jollie-fin/paillaas/board/prototype/motherboard_mini-itx_before_adding_io/motherboard_mini-itx.ods

Sheet: motherboard_mini-itx
Source: |  | /home/phi/dev/paillaaS/board/prototype/motherboard_mini-itx/motherboard_mini-itx.sch
Date: |  | mar. 13 avril 2021 10:53:32
Tool: |  | Eeschema 5.1.9-73d0e3b20d~88~ubuntu20.04.1
Generator: |  | /usr/share/kicad/plugins/bom_csv_grouped_by_value.py
Component Count: |  | 181
Individual Components:
Item |  | Qty |  |  |  |  | Reference(s) | Value | LibPart | Footprint | Datasheet
 |  |  |  |  |  |  | C1 | 100n | Device:C | Capacitor_SMD:C_0402_1005Metric | ~
 |  |  |  |  |  |  | C2 | 100n | Device:C | Capacitor_SMD:C_0402_1005Metric | ~
 |  |  |  |  |  |  | C3 | 100n | Device:C | Capacitor_SMD:C_0402_1005Metric | ~
 |  |  |  |  |  |  | C4 | 10u | Device:C | Capacitor_SMD:C_0402_1005Metric | ~
 |  |  |  |  |  |  | C5 | 100n | Device:C | Capacitor_SMD:C_0402_1005Metric | ~
 |  |  |  |  |  |  | C6 | 100n | Device:C | Capacitor_SMD:C_0402_1005Metric | ~
 |  |  |  |  |  |  | C7 | 100n | Device:C | Capacitor_SMD:C_0402_1005Metric | ~
 |  |  |  |  |  |  | C8 | 100n | Device:C | Capacitor_SMD:C_0402_1005Metric | ~
 |  |  |  |  |  |  | C9 | 10u | Device:C | Capacitor_SMD:C_0805_2012Metric | ~
 |  |  |  |  |  |  | C10 | 22n | Device:C | Capacitor_SMD:C_0402_1005Metric | ~
 |  |  |  |  |  |  | C11 | 100n | Device:C | Capacitor_SMD:C_0402_1005Metric | ~
 |  |  |  |  |  |  | C12 | 10u | Device:C | Capacitor_SMD:C_0805_2012Metric | ~
 |  |  |  |  |  |  | C13 | 100n | Device:C | Capacitor_SMD:C_0402_1005Metric | ~
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
 |  |  |  |  |  |  | D1 | RED | Device:LED | LED_SMD:LED_0603_1608Metric | ~
 |  |  |  |  |  |  | D2 | RED | Device:LED | LED_SMD:LED_0603_1608Metric | ~
 |  |  |  |  |  |  | D4 | RED | Device:LED | LED_SMD:LED_0603_1608Metric | ~
 |  |  |  |  |  |  | H1 | MountingHole_Pad | Mechanical:MountingHole_Pad | MountingHole:MountingHole_3.2mm_M3_Pad_Via | ~
 |  |  |  |  |  |  | H2 | MountingHole_Pad | Mechanical:MountingHole_Pad | MountingHole:MountingHole_3.2mm_M3_Pad_Via | ~
 |  |  |  |  |  |  | H3 | MountingHole_Pad | Mechanical:MountingHole_Pad | MountingHole:MountingHole_3.2mm_M3_Pad_Via | ~
 |  |  |  |  |  |  | H4 | MountingHole_Pad | Mechanical:MountingHole_Pad | MountingHole:MountingHole_3.2mm_M3_Pad_Via | ~
 |  |  |  |  |  |  | J1 | RJMG2310228A0ER | library:RJMG2310228A0ER | library:RJMG2310228A0ER | https://cdn.amphenol-icc.com/media/wysiwyg/files/documentation/datasheet/inputoutput/io_rjmag_stacked.pdf
 |  |  |  |  |  |  | J2 | Conn_01x22_MountingPin | Connector_Generic_MountingPin:Conn_01x22_MountingPin | Connector_FFC-FPC:TE_2-1734839-2_1x22-1MP_P0.5mm_Horizontal | ~
 |  |  |  |  |  |  | J3 | Conn_01x22_MountingPin | Connector_Generic_MountingPin:Conn_01x22_MountingPin | Connector_FFC-FPC:TE_2-1734839-2_1x22-1MP_P0.5mm_Horizontal | ~
 |  |  |  |  |  |  | J4 | Conn_02x20_Odd_Even | Connector_Generic:Conn_02x20_Odd_Even | Connector_IDC:IDC-Header_2x20_P2.54mm_Vertical | ~
 |  |  |  |  |  |  | J5 | Conn_02x08_Odd_Even | Connector_Generic:Conn_02x08_Odd_Even | Connector_PinHeader_2.54mm:PinHeader_2x08_P2.54mm_Vertical | ~
 |  |  |  |  |  |  | J6 | Conn_02x12_Top_Bottom | Connector_Generic:Conn_02x12_Top_Bottom | Connector_Molex:Molex_Mini-Fit_Jr_5566-24A_2x12_P4.20mm_Vertical | ~
 |  |  |  |  |  |  | J7 | Conn_02x04_Top_Bottom | Connector_Generic:Conn_02x04_Top_Bottom | Connector_Molex:Molex_Mini-Fit_Jr_5566-08A_2x04_P4.20mm_Vertical | ~
 |  |  |  |  |  |  | J8 | Conn_02x20_Odd_Even | Connector_Generic:Conn_02x20_Odd_Even | Connector_IDC:IDC-Header_2x20_P2.54mm_Vertical | ~
 |  |  |  |  |  |  | J9 | Conn_02x20_Odd_Even | Connector_Generic:Conn_02x20_Odd_Even | Connector_IDC:IDC-Header_2x20_P2.54mm_Vertical | ~
 |  |  |  |  |  |  | J10 | Conn_02x07_Odd_Even | Connector_Generic:Conn_02x07_Odd_Even | Connector_PinHeader_2.54mm:PinHeader_2x07_P2.54mm_Vertical | ~
 |  |  |  |  |  |  | J11 | Conn_01x22_MountingPin | Connector_Generic_MountingPin:Conn_01x22_MountingPin | Connector_FFC-FPC:TE_2-1734839-2_1x22-1MP_P0.5mm_Horizontal | ~
 |  |  |  |  |  |  | J12 | HDMI_A | Connector:HDMI_A | library:HDMI_RAHHD19TR | https://en.wikipedia.org/wiki/HDMI
 |  |  |  |  |  |  | J13 | USB_B_Micro | Connector:USB_B_Micro | Connector_USB:USB_Micro-B_Amphenol_10103594-0001LF_Horizontal | ~
 |  |  |  |  |  |  | R1 | 1k8 | Device:R | Resistor_SMD:R_0402_1005Metric | ~
 |  |  |  |  |  |  | R2 | 1k8 | Device:R | Resistor_SMD:R_0402_1005Metric | ~
 |  |  |  |  |  |  | R3 | 1k8 | Device:R | Resistor_SMD:R_0402_1005Metric | ~
 |  |  |  |  |  |  | R4 | 30 | Device:R | Resistor_SMD:R_0402_1005Metric | ~
 |  |  |  |  |  |  | R5 | 30 | Device:R | Resistor_SMD:R_0402_1005Metric | ~
 |  |  |  |  |  |  | R6 | 150 | Device:R | Resistor_SMD:R_0402_1005Metric | ~
 |  |  |  |  |  |  | R7 | 150 | Device:R | Resistor_SMD:R_0402_1005Metric | ~
 |  |  |  |  |  |  | R8 | 150 | Device:R | Resistor_SMD:R_0402_1005Metric | ~
 |  |  |  |  |  |  | R9 | 150 | Device:R | Resistor_SMD:R_0402_1005Metric | ~
 |  |  |  |  |  |  | R10 | 150 | Device:R | Resistor_SMD:R_0402_1005Metric | ~
 |  |  |  |  |  |  | R11 | 150 | Device:R | Resistor_SMD:R_0402_1005Metric | ~
 |  |  |  |  |  |  | R12 | 150 | Device:R | Resistor_SMD:R_0402_1005Metric | ~
 |  |  |  |  |  |  | R13 | 150 | Device:R | Resistor_SMD:R_0402_1005Metric | ~
 |  |  |  |  |  |  | R14 | 1K8 | Device:R | Resistor_SMD:R_0402_1005Metric | ~
 |  |  |  |  |  |  | R15 | 1K8 | Device:R | Resistor_SMD:R_0402_1005Metric | ~
 |  |  |  |  |  |  | R16 | 1k8 | Device:R | Resistor_SMD:R_0402_1005Metric | ~
 |  |  |  |  |  |  | R17 | 1K8 | Device:R | Resistor_SMD:R_0402_1005Metric | ~
 |  |  |  |  |  |  | R18 | 150 | Device:R | Resistor_SMD:R_0402_1005Metric | ~
 |  |  |  |  |  |  | R19 | 150 | Device:R | Resistor_SMD:R_0402_1005Metric | ~
 |  |  |  |  |  |  | R20 | 150 | Device:R | Resistor_SMD:R_0402_1005Metric | ~
 |  |  |  |  |  |  | R21 | 150 | Device:R | Resistor_SMD:R_0402_1005Metric | ~
 |  |  |  |  |  |  | R22 | 150 | Device:R | Resistor_SMD:R_0402_1005Metric | ~
 |  |  |  |  |  |  | R23 | 150 | Device:R | Resistor_SMD:R_0402_1005Metric | ~
 |  |  |  |  |  |  | R24 | 150 | Device:R | Resistor_SMD:R_0402_1005Metric | ~
 |  |  |  |  |  |  | R25 | 150 | Device:R | Resistor_SMD:R_0402_1005Metric | ~
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
 |  |  |  |  |  |  | R79 | 1k8 | Device:R | Resistor_SMD:R_0402_1005Metric | ~
 |  |  |  |  |  |  | R80 | 1k8 | Device:R | Resistor_SMD:R_0402_1005Metric | ~
 |  |  |  |  |  |  | R81 | 1k8 | Device:R | Resistor_SMD:R_0402_1005Metric | ~
 |  |  |  |  |  |  | R82 | 0.21 | Device:R | Resistor_SMD:R_1206_3216Metric | ~
 |  |  |  |  |  |  | SW1 | FSUSB30MUX | library:FSUSB30MUX | Package_SO:MSOP-10_3x3mm_P0.5mm | https://www.onsemi.com/pdf/datasheet/fsusb30-d.pdf
 |  |  |  |  |  |  | U1 | Compute_Module_4_Functional | Raspberry_Pi_Compute_Module_4:Compute_Module_4_Functional | RPi_Compute_Module_4:Raspberry-Pi-4-Compute-Module
 |  |  |  |  |  |  | U2 | 74LVC125 | 74xx:74LVC125 | Package_SO:TSSOP-14_4.4x5mm_P0.65mm | http://www.ti.com/lit/gpn/sn74LVC125
 |  |  |  |  |  |  | U3 | MCP3008 | Analog_ADC:MCP3008 | Package_SO:SOIC-16_3.9x9.9mm_P1.27mm | http://ww1.microchip.com/downloads/en/DeviceDoc/21295d.pdf
 |  |  |  |  |  |  | U4 | 74HCT244 | 74xx:74HC244 | Package_SO:TSSOP-20_4.4x6.5mm_P0.65mm | http://www.ti.com/lit/gpn/sn74LVC125
 |  |  |  |  |  |  | U5 | 74HCT244 | 74xx:74HC244 | Package_SO:TSSOP-20_4.4x6.5mm_P0.65mm | http://www.ti.com/lit/gpn/sn74LVC125
 |  |  |  |  |  |  | U6 | 74HC595 | 74xx:74HC595 | Package_SO:SSOP-16_5.3x6.2mm_P0.65mm | http://www.ti.com/lit/ds/symlink/sn74hc595.pdf
 |  |  |  |  |  |  | U7 | TBD62783A | Transistor_Array:TBD62783A | Package_SO:SSOP-18_4.4x6.5mm_P0.65mm | http://toshiba.semicon-storage.com/info/docget.jsp?did=30523&prodName=TBD62783APG
 |  |  |  |  |  |  | U8 | TMC5130A-TA | TMC5130:TMC5130A-TA | Package_QFP:TQFP-48-1EP_7x7mm_P0.5mm_EP5x5mm_ThermalVias
 |  |  |  |  |  |  | U9 | TMC5130A-TA | TMC5130:TMC5130A-TA | Package_QFP:TQFP-48-1EP_7x7mm_P0.5mm_EP5x5mm_ThermalVias
 |  |  |  |  |  |  | U10 | TMC5130A-TA | TMC5130:TMC5130A-TA | Package_QFP:TQFP-48-1EP_7x7mm_P0.5mm_EP5x5mm_ThermalVias
 |  |  |  |  |  |  | U11 | TMC5130A-TA | TMC5130:TMC5130A-TA | Package_QFP:TQFP-48-1EP_7x7mm_P0.5mm_EP5x5mm_ThermalVias
 |  |  |  |  |  |  | U12 | TMC5130A-TA | TMC5130:TMC5130A-TA | Package_QFP:TQFP-48-1EP_7x7mm_P0.5mm_EP5x5mm_ThermalVias
 |  |  |  |  |  |  | U13 | AP22804AW5 | Power_Management:AP22804AW5 | Package_TO_SOT_SMD:SOT-23-5 | https://www.diodes.com/assets/Datasheets/AP22804_14.pdf
Collated Components:
Item | Ppu | Qty |  | Subtotal | Accumul | Mouser | Reference(s) | Value | LibPart | Footprint | Datasheet
1 | 0.013 € | 26 | 26 | 0.34 € | 0.34 € | 581-0402YD104MAT2A | C1, C2, C3, C5, C6, C7, C8, C11, C13, C14, C17, C20, C22, C23, C26, C29, C31, C32, C35, C38, C40, C41, C44, C47, C49, C50 | 100n | Device:C | Capacitor_SMD:C_0402_1005Metric | ~
3 | 0.025 € | 28 | 28 | 0.70 € | 1.04 € | 963-EMK105BJ105KVHF | C4, C9, C12, C15, C16, C18, C21, C24, C25, C27, C30, C33, C34, C36, C39, C42, C43, C45, C48, C51, C52, C53, C54, C55, C56, C62, C63, C64 | 10u | Device:C | Capacitor_SMD:C_0805_2012Metric | ~
4 | 0.030 € | 6 | 6 | 0.18 € | 1.22 € | 80-C0603C223K5R | C10, C19, C28, C37, C46, C61 | 22n | Device:C | Capacitor_SMD:C_0402_1005Metric | ~
5 | 0.119 € | 5 | 5 | 0.60 € | 1.81 € | 140-REA101M1HBK0811P | C57, C58, C59, C60, C65 | 100u | Device:CP | Capacitor_THT:CP_Radial_D8.0mm_P3.50mm | ~
6 | 0.117 € | 3 | 3 | 0.35 € | 2.16 € | 710-150060GS75000 | D1, D2, D4 | RED | Device:LED | LED_SMD:LED_0603_1608Metric | ~
7 |  | 4 | 0 | 0.00 € | 2.16 € |  | H1, H2, H3, H4 | MountingHole_Pad | Mechanical:MountingHole_Pad | MountingHole:MountingHole_3.2mm_M3_Pad_Via | ~
8 | 3.450 € | 1 | 1 | 3.45 € | 5.61 € | 571-6116151-1 | J1 | RJMG2310228A0ER | library:RJMG2310228A0ER | library:RJMG2310228A0ER | https://cdn.amphenol-icc.com/media/wysiwyg/files/documentation/datasheet/inputoutput/io_rjmag_stacked.pdf
9 | 0.504 € | 3 | 3 | 1.51 € | 7.13 € | 538-501951-2230 | J2, J3, J11 | Conn_01x22_MountingPin | Connector_Generic_MountingPin:Conn_01x22_MountingPin | Connector_FFC-FPC:TE_2-1734839-2_1x22-1MP_P0.5mm_Horizontal | ~
10 | 0.932 € | 3 | 3 | 2.80 € | 9.92 € | 517-30340-6002 | J4, J8, J9 | Conn_02x20_Odd_Even | Connector_Generic:Conn_02x20_Odd_Even | Connector_IDC:IDC-Header_2x20_P2.54mm_Vertical | ~
11 |  | 1 | 0 | 0.00 € | 9.92 € |  | J5 | Conn_02x08_Odd_Even | Connector_Generic:Conn_02x08_Odd_Even | Connector_PinHeader_2.54mm:PinHeader_2x08_P2.54mm_Vertical | ~
12 | 0.966 € | 1 | 1 | 0.97 € | 10.89 € | 571-215860394 | J6 | Conn_02x12_Top_Bottom | Connector_Generic:Conn_02x12_Top_Bottom | Connector_Molex:Molex_Mini-Fit_Jr_5566-24A_2x12_P4.20mm_Vertical | ~
13 | 0.512 € | 1 | 1 | 0.51 € | 11.40 € | 571-15860398 | J7 | Conn_02x04_Top_Bottom | Connector_Generic:Conn_02x04_Top_Bottom | Connector_Molex:Molex_Mini-Fit_Jr_5566-08A_2x04_P4.20mm_Vertical | ~
14 |  | 1 | 0 | 0.00 € | 11.40 € |  | J10 | Conn_02x07_Odd_Even | Connector_Generic:Conn_02x07_Odd_Even | Connector_PinHeader_2.54mm:PinHeader_2x07_P2.54mm_Vertical | ~
15 | 0.529 € | 1 | 1 | 0.53 € | 11.93 € | 502-RAHHD19TR | J12 | HDMI_A | Connector:HDMI_A | library:HDMI_RAHHD19TR | https://en.wikipedia.org/wiki/HDMI
16 | 0.019 € | 1 | 1 | 0.02 € | 11.95 € |  | J13 | USB_B_Micro | Connector:USB_B_Micro | Connector_USB:USB_Micro-B_Amphenol_10103594-0001LF_Horizontal | ~
17 | 0.009 € | 32 | 32 | 0.29 € | 12.24 € |  | R1, R2, R3, R16, R38, R39, R41, R45, R46, R47, R48, R49, R53, R54, R55, R56, R57, R61, R62, R63, R64, R65, R69, R70, R71, R72, R73, R77, R78, R79, R80, R81 | 1k8 | Device:R | Resistor_SMD:R_0402_1005Metric | ~
18 | 0.019 € | 7 | 7 | 0.13 € | 12.37 € |  | R4, R5, R26, R27, R28, R29, R42 | 30 | Device:R | Resistor_SMD:R_0402_1005Metric | ~
19 | 0.009 € | 24 | 24 | 0.22 € | 12.59 € |  | R6, R7, R8, R9, R10, R11, R12, R13, R18, R19, R20, R21, R22, R23, R24, R25, R30, R31, R32, R33, R34, R35, R36, R37 | 150 | Device:R | Resistor_SMD:R_0402_1005Metric | ~
20 | 0.019 € | 4 | 4 | 0.08 € | 12.66 € |  | R14, R15, R17, R40 | 1K8 | Device:R | Resistor_SMD:R_0402_1005Metric | ~
21 | 0.019 € | 5 | 5 | 0.10 € | 12.76 € |  | R43, R51, R59, R67, R75 | 10 | Device:R | Resistor_SMD:R_0402_1005Metric | ~
22 | 0.058 € | 10 | 10 | 0.58 € | 13.34 € | 588-KDV12DR220ET | R44, R50, R52, R58, R60, R66, R68, R74, R76, R82 | 0.22 | Device:R | Resistor_SMD:R_1206_3216Metric | ~
23 | 0.445 € | 1 | 1 | 0.45 € | 13.78 € | 512-FSUSB30MUX | SW1 | FSUSB30MUX | library:FSUSB30MUX | Package_SO:MSOP-10_3x3mm_P0.5mm | https://www.onsemi.com/pdf/datasheet/fsusb30-d.pdf
24 | 1.820 € | 2 | 2 | 3.64 € | 17.42 € | 798-DF40HC30100DS451 | U1 | Compute_Module_4_Functional | Raspberry_Pi_Compute_Module_4:Compute_Module_4_Functional | RPi_Compute_Module_4:Raspberry-Pi-4-Compute-Module
25 | 1.950 € | 1 | 1 | 1.95 € | 19.37 € |  | U2 | 74LVC125 | 74xx:74LVC125 | Package_SO:TSSOP-14_4.4x5mm_P0.65mm | http://www.ti.com/lit/gpn/sn74LVC125
26 | 0.296 € | 1 | 1 | 0.30 € | 19.67 € |  | U3 | MCP3008 | Analog_ADC:MCP3008 | Package_SO:SOIC-16_3.9x9.9mm_P1.27mm | http://ww1.microchip.com/downloads/en/DeviceDoc/21295d.pdf
27 | 0.480 € | 2 | 2 | 0.96 € | 20.63 € |  | U4, U5 | 74HCT244 | 74xx:74HC244 | Package_SO:TSSOP-20_4.4x6.5mm_P0.65mm | http://www.ti.com/lit/gpn/sn74LVC125
28 | 0.500 € | 1 | 1 | 0.50 € | 21.13 € |  | U6 | 74HC595 | 74xx:74HC595 | Package_SO:SSOP-16_5.3x6.2mm_P0.65mm | http://www.ti.com/lit/ds/symlink/sn74hc595.pdf
29 | 1.400 € | 1 | 1 | 1.40 € | 22.53 € |  | U7 | TBD62783A | Transistor_Array:TBD62783A | Package_SO:SSOP-18_4.4x6.5mm_P0.65mm | http://toshiba.semicon-storage.com/info/docget.jsp?did=30523&prodName=TBD62783APG
30 | 4.270 € | 5 | 5 | 21.35 € | 43.88 € |  | U8, U9, U10, U11, U12 | TMC5130A-TA | TMC5130:TMC5130A-TA | Package_QFP:TQFP-48-1EP_7x7mm_P0.5mm_EP5x5mm_ThermalVias
31 | 0.338 € | 1 | 1 | 0.34 € | 44.22 € |  | U13 | AP22804AW5 | Power_Management:AP22804AW5 | Package_TO_SOT_SMD:SOT-23-5 | https://www.diodes.com/assets/Datasheets/AP22804_14.pdf
 |  |  | 176 | 44.22 €
 |  |  |  | 27

Sheet: Sheet2
 |  |  | Input
 |  |  | Nb | Price mouser | Nb parts | Nb components
 |  |  | 12 | 44.22 € | 27 | 176
PCB
width | height | area | Job fee | Price per area | Subtotal | Price per board
17 | 6.5 | 110.5 | 12.30 € | 0.185 € | 257.61 € | 21.47 €
Parts
Price mouser per board | Job fee | Handling fee | Subtotal | Price per board
44.22 € | 3.00 € | 20.00% | 639.70 € | 53.31 €
Stencil
Job fee | Price per area | Subtotal | Price per board
10.00 € | 0.095 € | 20.50 € | 1.71 €
Assembly
Job fee | Nb parts | Hand solder | Price per parts | Price of parts | Handling fee | Price handling | Nb components | Hand soldered comp | Placement fee | Price placement | Subtotal | Price per board
75.00 € | 27 | 4 | 4.50 € | 103.50 € | 0.01 € | 13.26 € | 171 | 6 | 0.05 € | 99.00 € | 290.76 € | 24.23 €
 |  |  | 23
 | Total | Price per board
 | 1,208.56 € | 100.71 €
 |  |  |  |  | PCB | Parts | Assembly | Stencil | Total
 |  |  |  |  | 21.32% | 52.93% | 24.06% | 1.70% | 100.00%
