jollie-fin/paillaas/board/prototype/usb2stepper/usb2stepper/usb2stepper_before_moving.kicad_pcb

## KiCad design board/prototype/usb2stepper/usb2stepper/usb2stepper_before_moving.kicad_pcb (2023-04-16)

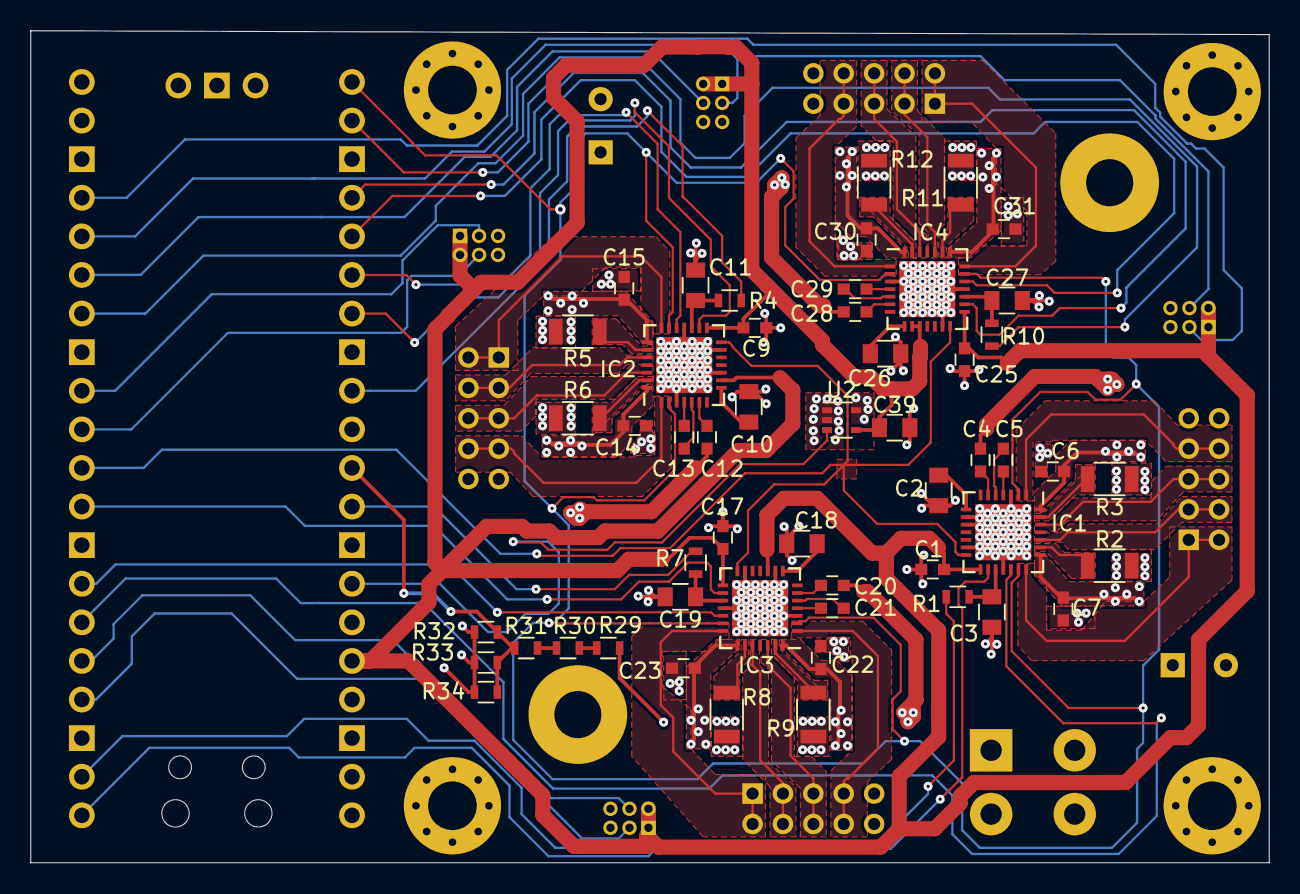
[picture p35: board usb2stepper_before_moving.kicad_pcb from above]

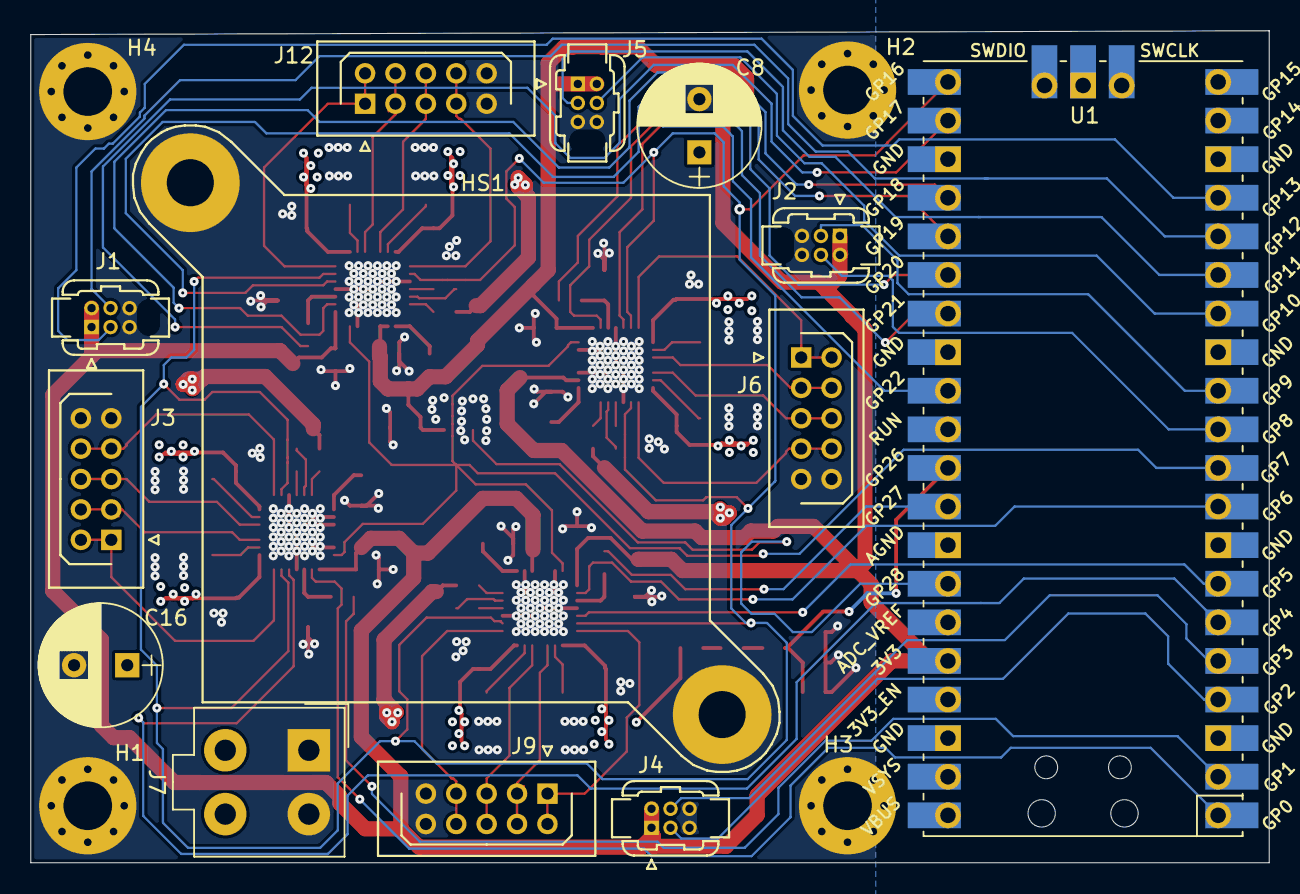
[picture p36: board usb2stepper_before_moving.kicad_pcb from below]

Board: 4 copper layers, 81.5 x 54.8 mm, 69 parts (17 on the bottom side), 73 nets.

Parts:
C1, C4, C6, C7, C9, C12, C14, C15, C17, C20, C22, C23, C25, C28, C30, C31: 100n; C_0603
C2, C3, C10, C11, C18, C19, C26, C27, C39: 2u2 16V; C_0805
C5, C13, C21, C29: 22n; C_0603
C8, C16: 100uF; CP_Radial_D8.0mm_P3.50mm
H1, H2, H3, H4: 3mm; MountingHole_3.2mm_M3_Pad_Via
HS1: 30x30mm; PCB_Heatsink_30x30mm_2xFixation3mm
IC1, IC2, IC3, IC4: TMC2209-LA; QFN-28-1EP_5x5mm_Pitch0.5mm_EP3.7x3.7
J1, J2, J4, J5: Conn_02x03_Odd_Even; Harwin_Gecko-G125-MVX0605L1X_2x03x1.25mm_Straight
J3, J6, J9, J12: Conn_02x05_Odd_Even; Harwin_LTek-Male_2x05x2.00mm_Straight
J7: Minifit_jr_2x2; Molex_MiniFit-JR-5556-04A_2x02x4.20mm_Straight
R1, R4, R7, R10, R29, R30, R31, R32, R33, R34: 10k; R_0603
R2, R3, R5, R6, R8, R9, R11, R12: 0.1; R_1206
U1: Pico; RPi_Pico_SMD_TH
U2: MCP9700AT-ELT; SOT-353_SC-70-5

Connections:
+3V3: C1.1, C9.1, C17.1, C25.1, C39.1, IC1.15, IC2.9, IC2.15, IC3.10, IC3.15, IC4.9, IC4.10, IC4.15, J1.1, J1.2, J2.1, J2.2, J4.1, J4.2, J5.1, J5.2, U1.36, U2.4
/24V_measure: R31.1, R32.2, R33.2, R34.2, U1.31
/DIR0: IC1.19, U1.6
/DIR1: IC2.19, U1.26
/DIR2: IC3.19, U1.7
/DIR3: IC4.19, U1.25
/DISABLE_MOT: IC1.2, IC1.20, IC2.2, IC2.20, IC3.2, IC3.20, IC4.2, IC4.20, U1.21
/REFL0: J1.3, U1.17
/REFL1: J2.3, U1.12
/REFL2: J4.3, U1.4
/REFL3: J5.3, U1.15
/REFR0: J1.4, U1.16
/REFR1: J2.4, U1.11
/REFR2: J4.4, U1.5
/REFR3: J5.4, U1.14
/STEP0: IC1.16, U1.1
/STEP1: IC2.16, U1.27
/STEP2: IC3.16, U1.9
/STEP3: IC4.16, U1.24
/Sheet608F6F9E/BRA: IC1.23, R2.2
/Sheet608F6F9E/BRB: IC1.27, R3.2
/Sheet608F6F9E/OA1: IC1.24, J3.3, J3.4
/Sheet608F6F9E/OA2: IC1.21, J3.1, J3.2
/Sheet608F6F9E/OB1: IC1.26, J3.5, J3.6
/Sheet608F6F9E/OB2: IC1.1, J3.7, J3.8
/Sheet608F6F9E/Vref: C3.1, IC1.17, R1.1
/TEMP: U1.34, U2.3
/UART: IC1.14, IC2.14, IC3.14, IC4.14, U1.10
/VREF_PWM0: R1.2, U1.2
/VREF_PWM1: R4.2, U1.29
/VREF_PWM2: R7.2, U1.32
/VREF_PWM3: R10.2, U1.22
/sheet6092AD70/BRA: IC4.23, R11.2
/sheet6092AD70/BRB: IC4.27, R12.2
/sheet6092AD70/OA1: IC4.24, J12.3, J12.4
/sheet6092AD70/OA2: IC4.21, J12.1, J12.2
/sheet6092AD70/OB1: IC4.26, J12.5, J12.6
/sheet6092AD70/OB2: IC4.1, J12.7, J12.8
/sheet6092AD70/Vref: C27.1, IC4.17, R10.1
/sheet609275BA/BRA: IC2.23, R5.2
/sheet609275BA/BRB: IC2.27, R6.2
/sheet609275BA/OA1: IC2.24, J6.3, J6.4
/sheet609275BA/OA2: IC2.21, J6.1, J6.2
/sheet609275BA/OB1: IC2.26, J6.5, J6.6
/sheet609275BA/OB2: IC2.1, J6.7, J6.8
/sheet609275BA/Vref: C11.1, IC2.17, R4.1
/sheet60929021/BRA: IC3.23, R8.2
/sheet60929021/BRB: IC3.27, R9.2
/sheet60929021/OA1: IC3.24, J9.3, J9.4
/sheet60929021/OA2: IC3.21, J9.1, J9.2
/sheet60929021/OB1: IC3.26, J9.5, J9.6
/sheet60929021/OB2: IC3.1, J9.7, J9.8
/sheet60929021/Vref: C19.1, IC3.17, R7.1
GND: C1.2, C2.2, C3.2, C6.2, C7.2, C8.2, C9.2, C10.2, C11.2, C14.2, C15.2, C16.2, C17.2, C18.2, C19.2, C22.2, C23.2, C25.2, C26.2, C27.2, C30.2, C31.2, C39.2, H1.1, H2.1, H3.1, H4.1, HS1.1, HS1.2, HS1.3, IC1.3, IC1.9, IC1.10, IC1.13, IC1.18, IC1.29, IC2.3, IC2.10, IC2.13, IC2.18, IC2.29, IC3.3, IC3.9, IC3.13, IC3.18, IC3.29, IC4.3, IC4.13, IC4.18, IC4.29, J1.5, J1.6, J2.5, J2.6, J3.9, J3.10, J4.5, J4.6, J5.5, J5.6, J6.9, J6.10, J7.1, J7.2, J9.9, J9.10, J12.9, J12.10, R2.1, R3.1, R5.1, R6.1, R8.1, R9.1, R11.1, R12.1, R32.1, R33.1, R34.1, U1.3, U1.8, U1.13, U1.18, U1.23, U1.28, U1.33, U1.38, U1.42, U2.1, U2.2, U2.5
unnamed: C2.1, IC1.8
unnamed: C4.2, IC1.6
unnamed: C5.1, IC1.5
unnamed: C5.2, IC1.4
unnamed: C10.1, IC2.8
unnamed: C12.2, IC2.6
unnamed: C13.1, IC2.5
unnamed: C13.2, IC2.4
unnamed: C18.1, IC3.8
unnamed: C20.2, IC3.6
unnamed: C21.1, IC3.5
unnamed: C21.2, IC3.4
unnamed: C26.1, IC4.8
unnamed: C28.2, IC4.6
unnamed: C29.1, IC4.5
unnamed: C29.2, IC4.4
unnamed: R29.1, R30.2
unnamed: R30.1, R31.2
Vdrive: C4.1, C6.1, C7.1, C8.1, C12.1, C14.1, C15.1, C16.1, C20.1, C22.1, C23.1, C28.1, C30.1, C31.1, IC1.22, IC1.28, IC2.22, IC2.28, IC3.22, IC3.28, IC4.22, IC4.28, J7.3, J7.4, R29.2
